hadoopmarc/hahaho-interactive-pole/doc/PCB-interactive-pole-corrections.jpg

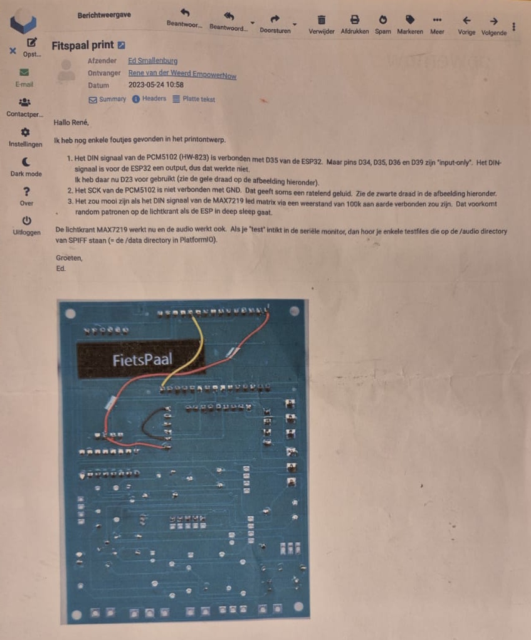
doc/PCB-interactive-pole-corrections.jpg
