hadoopmarc/hahaho-interactive-pole/kicad/driver-12V-1A-inverting/driver-12V-1A-inverting.png

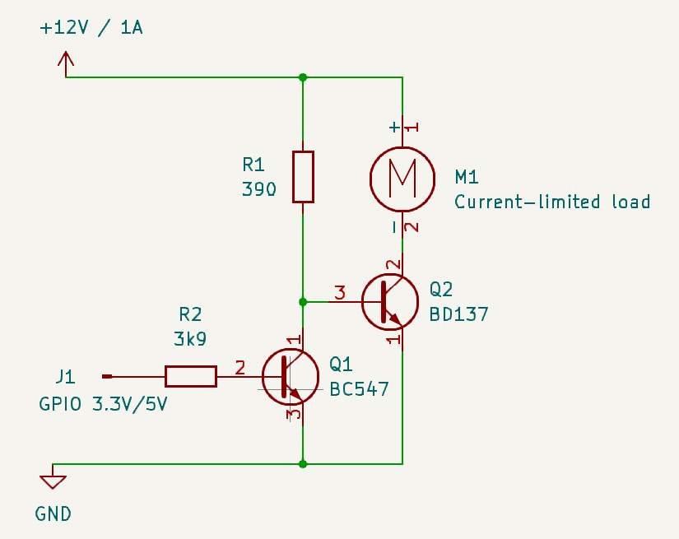
kicad/driver-12V-1A-inverting/driver-12V-1A-inverting.png
