hadoopmarc/hahaho-interactive-pole/doc/component-list-interactive-pole.jpg

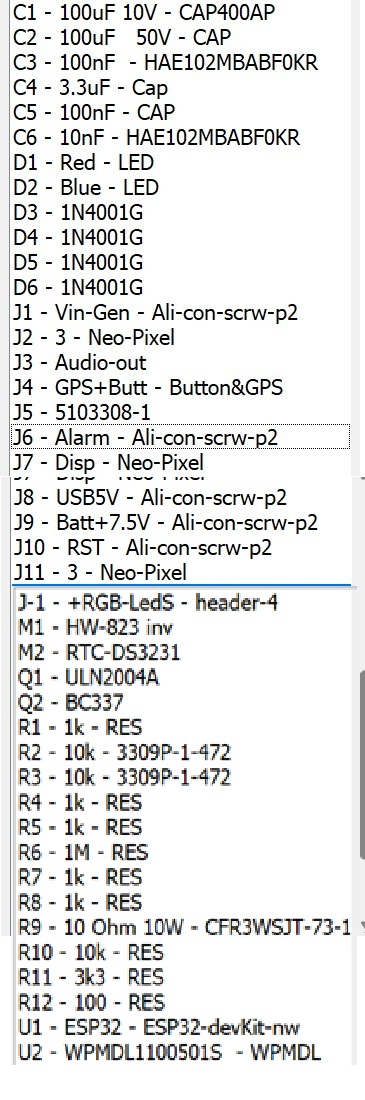
doc/component-list-interactive-pole.jpg
