hadoopmarc/hahaho-interactive-pole/standalone/control/webDash/webDash.ino

/*
  ------------------------
  ESP-DASH - Basic Example
  ------------------------

  Basic dashboard with some cards, filled with random data in real time.

  Github: https://github.com/ayushsharma82/ESP-DASH
  WiKi: https://docs.espdash.pro

  Works with ESP32, RP2040+W and RP2350+W based devices / projects.
  -------------------------------

  This can be used for the Interactive Pole to monitor sensor readings.
*/
#include <arduino.h>            // Only relevant for VSCode/PlatformIO Intellisense
#include <ESPAsyncWebServer.h>  // Install "ESP Aync WebServer" and "Async TCP" by ESP32Async
#include <ESPDash.h>
// See src/libraries/README.md for use in Arduino IDE
#include <secrets.h>
#include <pole_wifi.h>

/* Start Webserver */
AsyncWebServer server(80);

/* Attach ESP-DASH to AsyncWebServer */
char dashURI[] = "/dash";
ESPDash dashboard = ESPDash(server, dashURI, true);

/*
  Dashboard Cards
  Format - (Dashboard Instance, Card Type, Card Name, Card Symbol(optional) )
*/
dash::TemperatureCard temperature(dashboard, "Temperature");
dash::HumidityCard humidity(dashboard, "Humidity");

void setup() {
  Serial.begin(115200);
  wifi_setup(btnCredentials, btnCredsSize, &apCredentials);
  Serial.printf("Open webpage at %s\n", dashURI);

  /* Start AsyncWebServer */
  server.begin();
}

void loop() {
  /* Update Card Values */
  temperature.setValue((int)random(0, 50));
  humidity.setValue((int)random(0, 100));

  /* Send Updates to our Dashboard (realtime) */
  dashboard.sendUpdates();

  /*
    Delay is just for demonstration purposes in this example,
    Replace this code with 'millis interval' in your final project.
  */
  delay(3000);
}
