hadoopmarc/hahaho-interactive-pole/inspiration/src/charset.hpp

// charset2.hpp
// Character set for 8x8 display, turned -90 degrees
//
#if not defined ( _CHARSETHPP)
  #define _CHARSETHPP
  #define C_X     10                            // Special character "X"
  #define C_V     11                            // Special character "V"
  #define C_UP    12                            // Special character up-arrow
  #define C_RIGHT 13                            // Special character right arrow
  #define C_LEFT  14                            // Special character left arrow
  #define C_DOWN  15                            // Special character down arrow
  #define C_BUT   16                            // Special character button
/*
  uint64_t charsetx[] =
    {
      //  1       2       3       4       5       6       7       8
      //  Down    Up      Down    Up      Down    Up      Down    Up
      //  ........--------........--------........--------........--------  
        0b0011110001000010100000011000000110000001100000010100001000111100,   // 0
        0b0000110001010000000010000001000000001000000100000000100011111111,   // 1
        0b0111111010000001100000000000011000011000011000011000000111111111,   // 2
        0b0111111010000001100000010000111010000000100000011000000101111110,   // 3
        0b0110000000001010010010000010001001000010111111110100000000000111,   // 4
        0b1111111110000001000000011111111010000000100000011000000101111110,   // 5
        0b0111111010000001000000011000000001111111100000011000000101111110,   // 6
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
        0b0000110000011000001100000110000001100000001100000001100000001100,   // <
        0b0001100000011000000110000001100010011001010110100011110000011000,   // down arrow
        0b0011110001111110111111111111111101111110011111100111111000000000    // button
    } ;

#endif
